pentolope/PCBA_StatusBeacon/design/evidence.py

from __future__ import annotations

import hashlib
import json
import os
import sys

REPO_ROOT = os.path.dirname(os.path.dirname(os.path.abspath(__file__)))
INDEX_PATH = os.path.join(REPO_ROOT, "evidence", "index.json")
DATASHEET_DIR = os.path.join(REPO_ROOT, "evidence", "datasheets")

SOURCES = {
    "ws2812b_v5_worldsemi": {
        "file": "datasheets/ws2812b_v5_worldsemi.pdf",
        "url": "https://wmsc.lcsc.com/wmsc/upload/file/pdf/v2/lcsc/"
               "2304140030_Worldsemi-WS2812B-V5-W_C2874885.pdf",
        "retrieved": "2026-09-02",
        "applies_to": ["WS2812B-V5/W"],
    },
    "mlcc_samsung": {
        "file": "datasheets/mlcc_samsung.pdf",
        "url": "https://datasheet.lcsc.com/datasheet/pdf/"
               "02336ea48ea44ca18c72517dd3cb7b47.pdf",
        "retrieved": "2026-09-10",
        "document_id": "Samsung Electro-Mechanics Multilayer Ceramic "
                       "Capacitors, November 2015",
        "applies_to": ["CL05B104KO5NNNC", "CL21A475KAQNNNE"],
    },
    "me6211_microne": {
        "file": "datasheets/me6211_microne.pdf",
        "url": "https://wmsc.lcsc.com/wmsc/upload/file/pdf/v2/lcsc/"
               "2304140030_MICRONE-Nanjing-Micro-One-Elec-"
               "ME6211C50M5G-N_C236670.pdf",
        "retrieved": "2026-09-02",
        "applies_to": ["ME6211C50M5G-N"],
    },
    "py32f003_puya": {
        "file": "datasheets/py32f003_puya.pdf",
        "url": "https://download.py32.org/Datasheet/en/"
               "PY32F003_Datasheet_Rev1.7.pdf",
        "retrieved": "2026-09-01",
        "document_id": "PY32F003 Datasheet Rev1.7",
        "applies_to": ["PY32F003F18P6TU"],
    },
    "tpd1e10b06_ti": {
        "file": "datasheets/tpd1e10b06_ti.pdf",
        "url": "https://www.ti.com/lit/ds/symlink/tpd1e10b06.pdf",
        "retrieved": "2026-09-01",
        "document_id": "SLLSEB1G",
        "applies_to": ["TPD1E10B06DPYR"],
    },
    "typec31m12_hro": {
        "file": "datasheets/typec31m12_hro.pdf",
        "url": "https://wmsc.lcsc.com/wmsc/upload/file/pdf/v2/lcsc/"
               "2205251630_Korean-Hroparts-Elec-TYPE-C-31-M-12_C165948.pdf",
        "retrieved": "2026-09-01",
        "applies_to": ["TYPE-C-31-M-12"],
    },
    "typec31m12_lcsc_landpattern": {
        "file": "datasheets/typec31m12_lcsc_landpattern.json",
        "url": "https://easyeda.com/api/products/C165948/svgs",
        "retrieved": "2026-09-01",
        "document_id": "LCSC C165948 footprint, docType 4",
        "applies_to": ["TYPE-C-31-M-12"],
    },
    "chip_resistor_uniroyal": {
        "file": "datasheets/chip_resistor_uniroyal.pdf",
        "url": "https://datasheet.lcsc.com/datasheet/pdf/"
               "0a975aaa49b7c97f38a963127be4a823.pdf",
        "retrieved": "2026-09-10",
        "document_id": "Uniroyal Thick Film Chip Resistors Feb.12,2019 V.3",
        "applies_to": ["0402WGF1001TCE", "0402WGF1002TCE",
                       "0402WGF330JTCE", "0402WGF5101TCE"],
    },
    "k2_1187sq_hro": {
        "file": "datasheets/k2_1187sq_hro.pdf",
        "url": "https://wmsc.lcsc.com/wmsc/upload/file/pdf/v2/lcsc/"
               "2304140030_Korean-Hroparts-Elec-K2-1187SQ-A4SW-06_C92584.pdf",
        "retrieved": "2026-09-01",
        "applies_to": ["K2-1187SQ-A4SW-06"],
    },
}


def digest(path):
    hasher = hashlib.sha256()
    with open(path, "rb") as handle:
        for chunk in iter(lambda: handle.read(1 << 16), b""):
            hasher.update(chunk)
    return hasher.hexdigest()


def compute_index():
    entries = {}
    for name in sorted(SOURCES):
        source = SOURCES[name]
        path = os.path.join(REPO_ROOT, "evidence", source["file"])
        entry = dict(source)
        entry["sha256"] = digest(path)
        entry["bytes"] = os.path.getsize(path)
        entries[name] = entry
    return {"schema_version": 1, "documents": entries}


def load_index():
    with open(INDEX_PATH, "r", encoding="utf-8") as handle:
        return json.load(handle)


def write_index():
    with open(INDEX_PATH, "w", encoding="utf-8", newline="\n") as handle:
        json.dump(compute_index(), handle, indent=2, sort_keys=True)
        handle.write("\n")
    return INDEX_PATH


def verify():
    recorded = load_index()["documents"]
    present = {
        name for name in os.listdir(DATASHEET_DIR)
        if name.endswith((".pdf", ".json"))}
    referenced = {os.path.basename(entry["file"])
                  for entry in recorded.values()}
    problems = []
    for name in sorted(referenced - present):
        problems.append(("missing_file", name))
    for name in sorted(present - referenced):
        problems.append(("unreferenced_file", name))
    for name in sorted(recorded):
        entry = recorded[name]
        path = os.path.join(REPO_ROOT, "evidence", entry["file"])
        if not os.path.isfile(path):
            continue
        if digest(path) != entry["sha256"]:
            problems.append(("digest_mismatch", name))
    return problems


if __name__ == "__main__":
    sys.stdout.write(write_index() + "\n")
