pentolope/PCBA_StatusBeacon/design/build.py

from __future__ import annotations

import json
import os
import sys

from . import netlist, schematic

REPO_ROOT = os.path.dirname(os.path.dirname(os.path.abspath(__file__)))


def schematic_path():
    return os.path.join(REPO_ROOT, netlist.PROJECT_NAME + ".kicad_sch")


def project_path():
    return os.path.join(REPO_ROOT, netlist.PROJECT_NAME + ".kicad_pro")


def generate_schematic_text():
    netlist.pin_to_net()
    tree = schematic.build(
        netlist.PARTS, netlist.NETS, set(netlist.NO_CONNECT),
        netlist.PROJECT_NAME)
    return schematic.render(tree)


def project_document(root_sheet_uuid):
    return {
        "board": {
            "design_settings": {
                "rule_severities": {
                    "missing_courtyard": "warning",
                    "track_not_centered_on_via": "warning",
                    "tuning_profile_track_geometries": "warning",
                    "footprint_filters_mismatch": "warning",
                    "footprint_type_mismatch": "warning",
                },
                "rules": {
                    "min_clearance": 0.15,
                    "min_track_width": 0.15,
                    "min_via_diameter": 0.45,
                    "min_via_annular_width": 0.1,
                    "min_through_hole_diameter": 0.25,
                    "min_hole_clearance": 0.25,
                    "min_hole_to_hole": 0.25,
                    "min_copper_edge_clearance": 0.3,
                },
            },
            "drc_exclusions": [],
            "layer_presets": [],
            "viewports": [],
        },
        "boards": [],
        "cvpcb": {"equivalence_files": []},
        "erc": {
            "erc_exclusions": [],
            "meta": {"version": 0},
            "pin_map": [],
            "rule_severities": {
                "single_global_label": "warning",
                "four_way_junction": "warning",
                "simulation_model_issue": "warning",
                "footprint_filter": "warning",
            },
        },
        "libraries": {"pinned_footprint_libs": [], "pinned_symbol_libs": []},
        "meta": {"filename": netlist.PROJECT_NAME + ".kicad_pro",
                 "version": 3},
        "net_settings": {
            "classes": [{
                "name": "Default",
                "clearance": 0.15,
                "track_width": 0.25,
                "via_diameter": 0.6,
                "via_drill": 0.3,
            }],
        },
        "pcbnew": {"last_paths": {}, "page_layout_descr_file": ""},
        "schematic": {"legacy_lib_dir": "", "legacy_lib_list": []},
        "sheets": [[root_sheet_uuid, "Root"]],
        "text_variables": {},
    }


def write_project():
    root_uuid = str(schematic._uuid("sheet", netlist.PROJECT_NAME))
    with open(project_path(), "w", encoding="utf-8", newline="\n") as handle:
        json.dump(project_document(root_uuid), handle, indent=2)
        handle.write("\n")
    return project_path()


def write():
    text = generate_schematic_text()
    with open(schematic_path(), "w", encoding="utf-8", newline="\n") as handle:
        handle.write(text)
    root_uuid = str(
        schematic._uuid("sheet", netlist.PROJECT_NAME))
    with open(project_path(), "w", encoding="utf-8", newline="\n") as handle:
        json.dump(project_document(root_uuid), handle, indent=2)
        handle.write("\n")
    return schematic_path(), project_path()


if __name__ == "__main__":
    for path in write():
        sys.stdout.write(path + "\n")
