pentolope/PCBA_StatusBeacon/design/simulation.py

from __future__ import annotations

import json
import os
import sys

from . import layout, netlist

REPO_ROOT = layout.REPO_ROOT
SIM_DIR = os.path.join(REPO_ROOT, "sim")
PARAMETERS_PATH = os.path.join(REPO_ROOT, "components", "parameters.json")

#: The name the manifest registers the extracted copper model under. The
#: measured identity embeds the board digest, so only an alias can be
#: written into a stored scenario.
EXTRACTED_MODEL_ALIAS = "led_data_copper"

SUPPLY_PATH_BUDGET_OHM = 0.1
MCU_INPUT_CAPACITANCE_F = 5e-12


def shortest_high_s(parameters):
    return led(parameters)["data_timing"]["shortest_high_s"]["value"]


def _spec(parameters, reference):
    """The frozen parameters of whatever part the netlist selects.

    Keyed through the netlist rather than by a literal MPN, so replacing
    a part is one edit in one place and cannot leave a stale key here.
    """
    return parameters["parts"][netlist.PARTS[reference]["mpn"]]


def led(parameters):
    return _spec(parameters, "D1")


def mcu(parameters):
    return _spec(parameters, "U1")


def led_input_capacitance_f(parameters):
    return led(parameters)["digital_inputs"]["4"]["input_capacitance_f"][
        "value"]


def _parameters():
    with open(PARAMETERS_PATH, encoding="utf-8") as handle:
        return json.load(handle)


def _sum_capacitance(net):
    total = 0.0
    for pin_ref in netlist.NETS[net]:
        reference = pin_ref.split(".", 1)[0]
        part = netlist.PARTS.get(reference)
        if part is None or not reference.startswith("C"):
            continue
        value = part["value"]
        if value.endswith("uF"):
            total += float(value[:-2]) * 1e-6
        elif value.endswith("nF"):
            total += float(value[:-2]) * 1e-9
        else:
            raise ValueError("capacitor {} carries the unparsable value "
                             "{!r}".format(reference, value))
    return total


def _resistor_ohms(reference):
    value = netlist.PARTS[reference]["value"]
    if value.endswith("k"):
        return float(value[:-1]) * 1e3
    if value.endswith("R"):
        return float(value[:-1])
    raise ValueError("resistor {} carries the unparsable value {!r}".format(
        reference, value))


def _board_digest(path):
    hasher = hashlib.sha256()
    with open(path, "rb") as handle:
        for chunk in iter(lambda: handle.read(1 << 16), b""):
            hasher.update(chunk)
    return hasher.hexdigest()


def _ideal(records):
    return {name: {"stands_in_for": detail,
                   "accepted_for_design_decision": True}
            for name, detail in records.items()}


def _measurement(name, kind, node, op, value):
    return {"name": name, "kind": kind, "node": node,
            "assertion": {"op": op, "value": value}}


def rail_droop_scenario(parameters):
    spec = led(parameters)
    # The rail is the regulator's output. Driving the scenario at the low end
    # of the declared rail - the source minimum less the dropout the regulator
    # shows at the declared port budget - makes every rail voltage it reports
    # a LOWER BOUND on the real one, which is the direction a ">=" assertion
    # needs.
    source_v = netlist.RAILS["+5V"]["min_v"]
    step_a = (netlist.LED_COUNT * spec["supply_current_max_a"]["value"]
              * netlist.FIRMWARE_GLOBAL_BRIGHTNESS_LIMIT)
    bound = {"kind": "lower_bound",
             "basis": {"kind": "assumed",
                       "detail": "the rail is held at the low end of its "
                                 "declared range, the source minimum less "
                                 "the regulator's dropout at the declared "
                                 "port budget, so it can only be higher "
                                 "than this in service"}}
    return {
        "name": "rail_droop_on_led_turn_on",
        "elements": [
            {"kind": "vsource_dc", "name": "SRC", "nodes": ["src", "0"],
             "value": source_v},
            {"kind": "resistor", "name": "RPATH", "nodes": ["src", "rail"],
             "value": SUPPLY_PATH_BUDGET_OHM},
            {"kind": "capacitor", "name": "CBULK", "nodes": ["rail", "0"],
             "value": _sum_capacitance("+5V")},
            {"kind": "resistor", "name": "RLED", "nodes": ["rail", "sink"],
             "value": source_v / step_a},
            {"kind": "vsource_pulse", "name": "SWITCH",
             "nodes": ["sink", "0"],
             "pulse": {"v1": source_v, "v2": 0.0, "delay_s": 1e-4,
                       "rise_s": 1e-9, "fall_s": 1e-9, "width_s": 1e-3,
                       "period_s": 2e-3}},
        ],
        "analyses": [{"kind": "tran", "step_s": 1e-7, "stop_s": 1.1e-3}],
        "measurements": [
            dict(_measurement("rail_excursion_min", "tran_min_voltage",
                              "rail", ">=",
                              spec["supply"]["abs_min_v"]["value"]),
                 knowledge=bound),
            {"name": "rail_excursion_max", "kind": "tran_max_voltage",
             "node": "rail", "knowledge": bound},
        ],
        "assumptions": _ideal({
            "SRC": "the regulator's output at the low end of the declared "
                   "rail, as an ideal source; its transient response to a "
                   "load step is not modelled, and the datasheet states no "
                   "load-transient figure to model it from",
            "RPATH": "the series resistance of the cable, the receptacle "
                     "contacts and the board copper between the receptacle "
                     "and the LED ring, as a design budget",
            "CBULK": "every bulk and decoupling capacitance on the rail as "
                     "one ideal capacitor, with no ESR, no ESL and no DC "
                     "bias derating",
            "RLED": "the LED array's aggregate draw as a fixed resistance "
                    "at its worst-case current; a constant-current load "
                    "droops no further than this",
            "SWITCH": "the instant at which firmware turns the whole ring "
                      "on, as an ideal switch with no on-resistance",
        }),
    }


def button_release_scenario(parameters):
    spec = mcu(parameters)
    rail_v = netlist.RAILS["+5V"]["max_v"]
    vih = spec["digital_inputs"]["19"]["vih_min"]["factor_of_supply"] * rail_v
    return {
        "name": "button_release_detection",
        "elements": [
            {"kind": "vsource_pulse", "name": "RAIL", "nodes": ["rail", "0"],
             "pulse": {"v1": 0.0, "v2": rail_v, "delay_s": 0.0,
                       "rise_s": 1e-9, "fall_s": 1e-9,
                       "width_s": netlist.BUTTON_RELEASE_DETECT_S,
                       "period_s": 2 * netlist.BUTTON_RELEASE_DETECT_S}},
            {"kind": "resistor", "name": "RPULLUP", "nodes": ["rail", "btn"],
             "value": _resistor_ohms("R6")},
            {"kind": "capacitor", "name": "CFILTER", "nodes": ["btn", "0"],
             "value": _sum_capacitance("BTN_SW")},
            {"kind": "resistor", "name": "RSERIES", "nodes": ["btn", "mcu"],
             "value": _resistor_ohms("R5")},
            {"kind": "capacitor", "name": "CPIN", "nodes": ["mcu", "0"],
             "value": MCU_INPUT_CAPACITANCE_F},
        ],
        "analyses": [{"kind": "tran", "step_s": 1e-6,
                      "stop_s": netlist.BUTTON_RELEASE_DETECT_S}],
        "measurements": [
            _measurement("mcu_input_at_deadline", "tran_final_voltage", "mcu",
                         ">=", vih),
            _measurement("mcu_input_peak", "tran_max_voltage", "mcu",
                         "<=", spec["supply"]["characterised_max_v"]["value"]),
        ],
        "assumptions": _ideal({
            "RAIL": "the switch contact held closed long enough for the "
                    "filter capacitor to reach the reference node, then "
                    "opening at t=0; stepping the pull-up's source is the "
                    "same waveform as releasing the contact",
            "RPULLUP": "the pull-up resistor at its nominal value, with no "
                       "tolerance and no temperature coefficient",
            "CFILTER": "the debounce capacitance as an ideal capacitor, "
                       "with no ESR and no DC bias derating",
            "RSERIES": "the series protection resistor at its nominal "
                       "value",
            "CPIN": "the MCU input pin's capacitance and the ESD clamp's "
                    "off-state loading",
        }),
    }


def led_data_edge_scenario(parameters, model_identity=None):
    """The shortest protocol high time, driven through the series resistor.

    Two forms of the same question. Without an extracted model the
    interconnect is an ideal wire and every series value is a nominal
    component value, so the node voltage is exact and the receiver
    threshold is decidable. With the extracted model the copper carries a
    LOWER-bound resistance - the extraction omits via barrel resistance -
    and a larger series resistance can only lower the node voltage, so the
    simulated value bounds the true one from ABOVE. An upper bound settles
    "never exceeds the absolute maximum" and cannot settle "reaches the
    input threshold", so each form asserts only what its evidence carries.
    """
    driver = mcu(parameters)
    receiver = led(parameters)
    rail_v = netlist.RAILS["+5V"]["max_v"]
    voh = rail_v + driver["digital_outputs"]["20"]["voh_min"][
        "offset_from_supply"]
    vih = receiver["digital_inputs"]["4"]["vih_min"]["factor_of_supply"] * rail_v
    extracted = model_identity is not None
    driver_node = "rin" if not extracted else "drv"
    elements = [
        {"kind": "vsource_pulse", "name": "DRIVER",
         "nodes": [driver_node, "0"],
         "pulse": {"v1": 0.0, "v2": voh, "delay_s": 0.0,
                   "rise_s": 1e-9, "fall_s": 1e-9,
                   "width_s": shortest_high_s(parameters),
                   "period_s": 2 * shortest_high_s(parameters)}},
    ]
    if extracted:
        elements.append({"kind": "model_instance", "name": "COPPER",
                         "nodes": ["drv", "rin"], "model": model_identity})
    elements.extend([
        {"kind": "resistor", "name": "RSERIES", "nodes": ["rin", "din"],
         "value": _resistor_ohms("R4")},
        {"kind": "capacitor", "name": "CDIN", "nodes": ["din", "0"],
         "value": led_input_capacitance_f(parameters)},
    ])
    ideal = {
        "DRIVER": "the MCU output as an ideal source stepping to its "
                  "worst-case output high level, with no output impedance "
                  "and no package parasitics",
        "RSERIES": "the series termination resistor at its nominal value",
        "CDIN": "the LED data input's capacitance and the ESD clamp's "
                "off-state loading",
    }
    scenario = {
        "name": ("led_data_edge_over_extracted_copper" if extracted
                 else "led_data_edge_over_ideal_interconnect"),
        "elements": elements,
        "analyses": [{"kind": "tran", "step_s": 1e-10,
                      "stop_s": shortest_high_s(parameters)}],
        "assumptions": _ideal(ideal),
    }
    if not extracted:
        scenario["measurements"] = [
            _measurement("din_at_shortest_high_end", "tran_final_voltage",
                         "din", ">=", vih),
            _measurement("din_peak", "tran_max_voltage", "din", "<=",
                         receiver["supply"]["abs_max_v"]["value"]),
        ]
        return scenario
    bound = {
        "kind": "upper_bound",
        "basis": {
            "kind": "assumed",
            "detail": "the extracted copper resistance is a lower bound - "
                      "via barrel resistance is omitted by the extraction - "
                      "and the node voltage falls monotonically with series "
                      "resistance, so the simulated value bounds the true "
                      "one from above",
        },
    }
    peak = _measurement("din_peak", "tran_max_voltage", "din", "<=",
                        receiver["supply"]["abs_max_v"]["value"])
    peak["knowledge"] = bound
    settled = {"name": "din_at_shortest_high_end",
               "kind": "tran_final_voltage", "node": "din",
               "knowledge": bound}
    scenario["measurements"] = [peak, settled]
    scenario["required_coverage"] = {
        "interconnect_dc": ["geometry-derived", "quasi-static-extracted",
                            "full-wave-extracted", "measured"]}
    return scenario


def _write(path, document):
    os.makedirs(os.path.dirname(path), exist_ok=True)
    with open(path, "w", encoding="utf-8", newline="\n") as handle:
        json.dump(document, handle, indent=2, sort_keys=True)
        handle.write("\n")
    return path


def write():
    parameters = _parameters()
    written = []
    for name, document in (
            ("pre_layout_rail_droop.json", rail_droop_scenario(parameters)),
            ("pre_layout_button_release.json",
             button_release_scenario(parameters)),
            ("pre_layout_led_data_edge.json",
             led_data_edge_scenario(parameters)),
            ("post_layout_led_data_edge.json",
             led_data_edge_scenario(parameters, EXTRACTED_MODEL_ALIAS))):
        written.append(_write(os.path.join(SIM_DIR, name), document))
    return written


if __name__ == "__main__":
    for written in write():
        sys.stdout.write(written + "\n")
